uq-flor-pro/florence-player/docs/assets/dimensions2.png

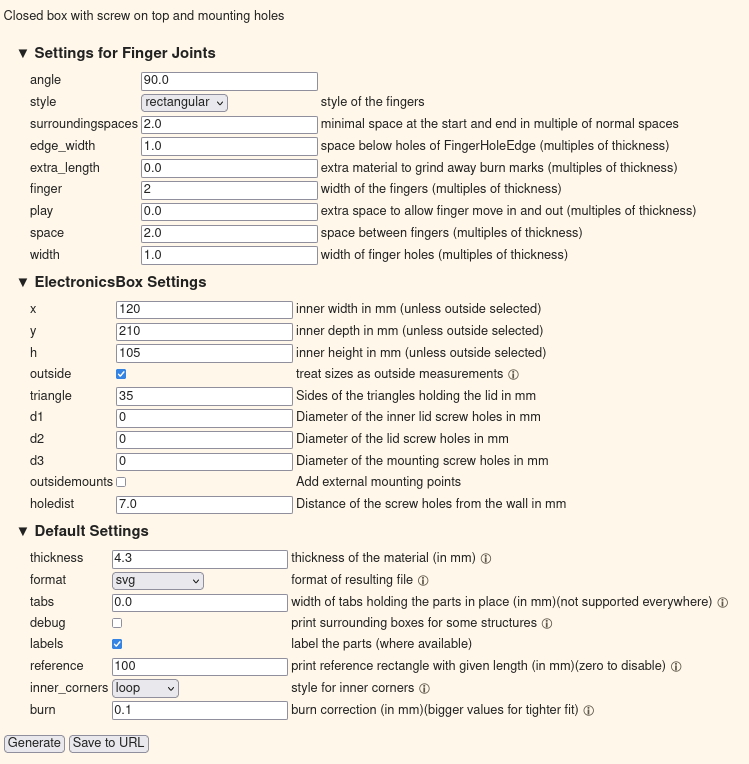
docs/assets/dimensions2.png
