uq-flor-pro/florence-player/docs/assets/front_mounted.jpg

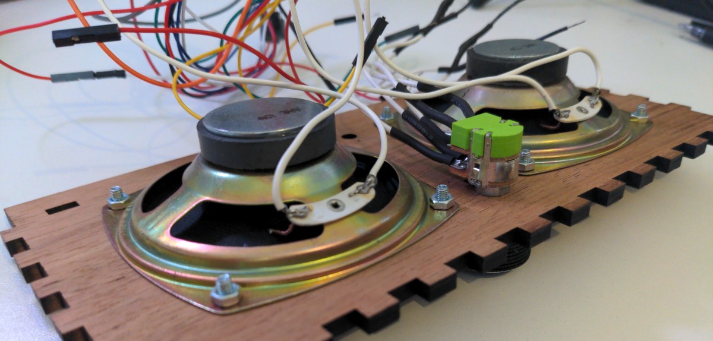
docs/assets/front_mounted.jpg
