uq-flor-pro/florence-player/docs/assets/mount_top.jpg

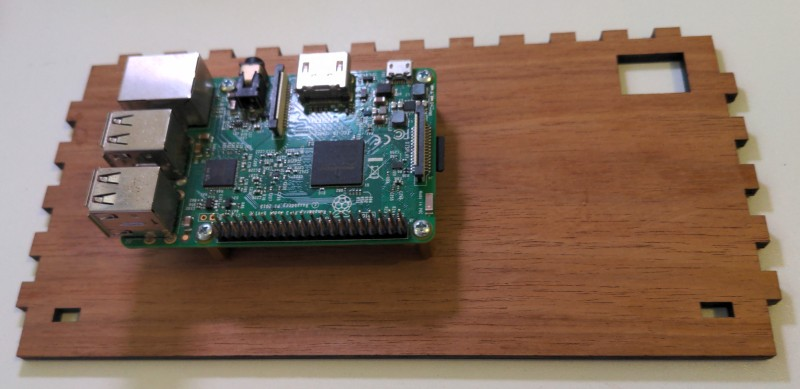
docs/assets/mount_top.jpg
