uq-flor-pro/florence-player/docs/assets/pot_mount.jpg

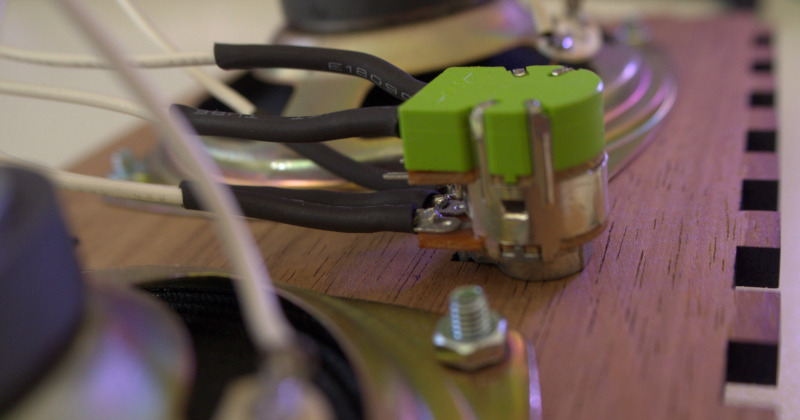
docs/assets/pot_mount.jpg
